wak-lab-e-v/WEMOS-D1-WS2812b-CTRL/Datasheet/LM2596.jpg

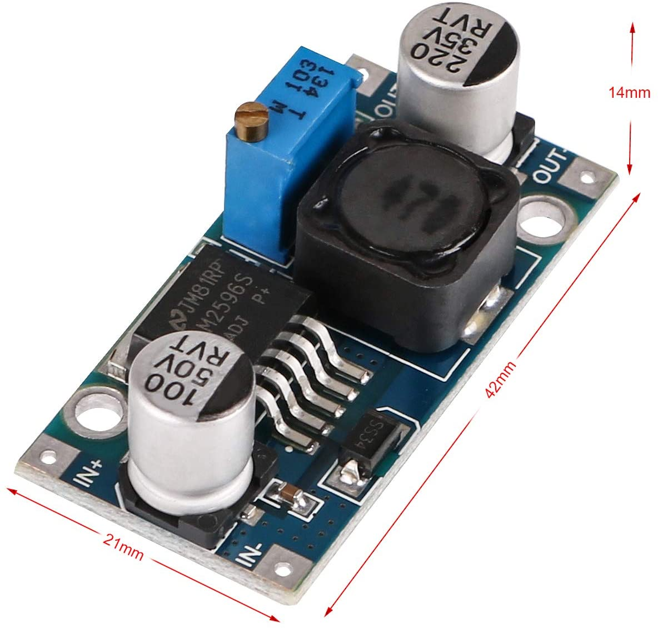
Datasheet/LM2596.jpg
