wak-lab-e-v/WEMOS-D1-WS2812b-CTRL/fritzing/PCB Export/ESP-LED-CTRL_etch_silk_bottom.pdf

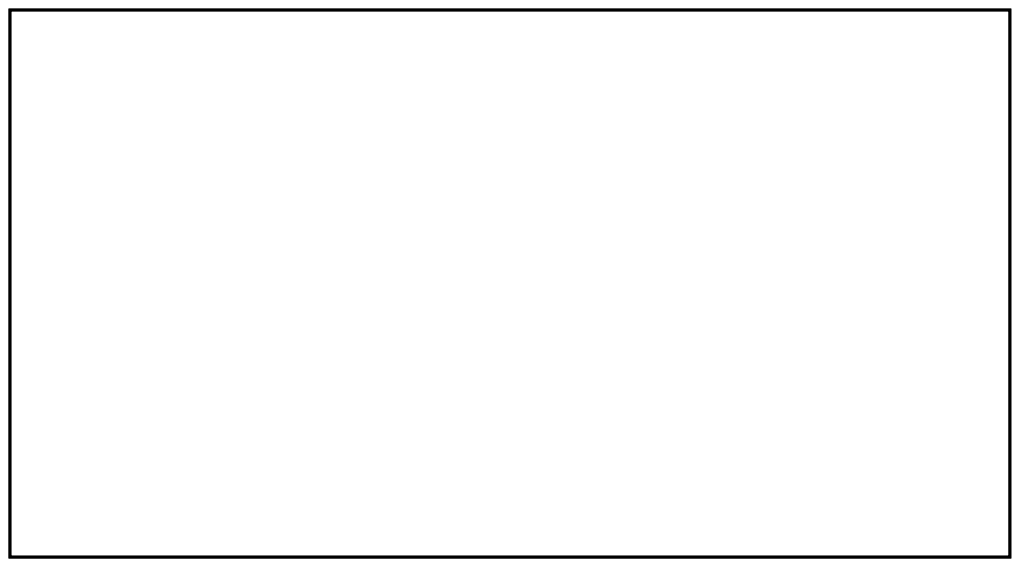
[picture p19: page 1]
