wak-lab-e-v/WEMOS-D1-WS2812b-CTRL/fritzing/PCB Export/ESP-LED-CTRL_etch_silk_top.pdf

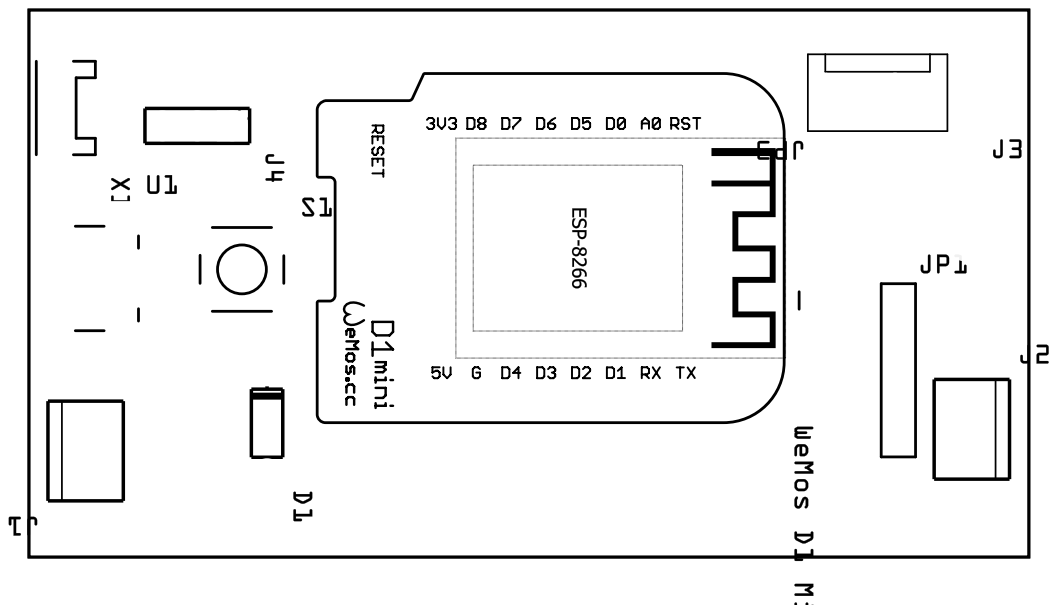
[picture p21: page 1]
