wak-lab-e-v/WEMOS-D1-WS2812b-CTRL/fritzing/PCB Export/ESP-LED-CTRL_etch_silk_top_mirror.pdf

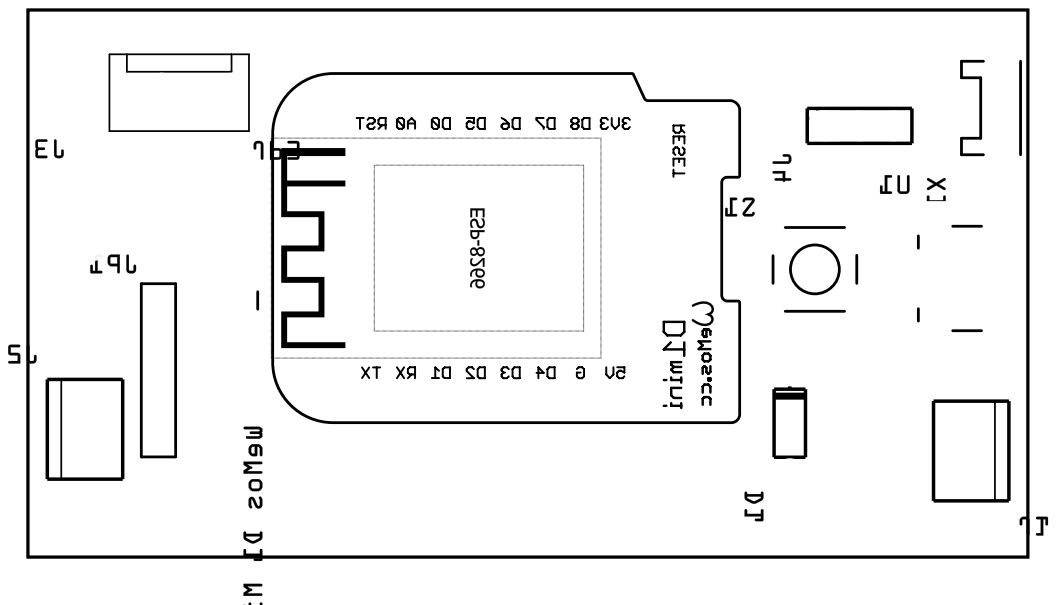
[picture p22: page 1]
